FriBox/Air-Sensor/HardWare/ESP32-D0WDQ6-1.png

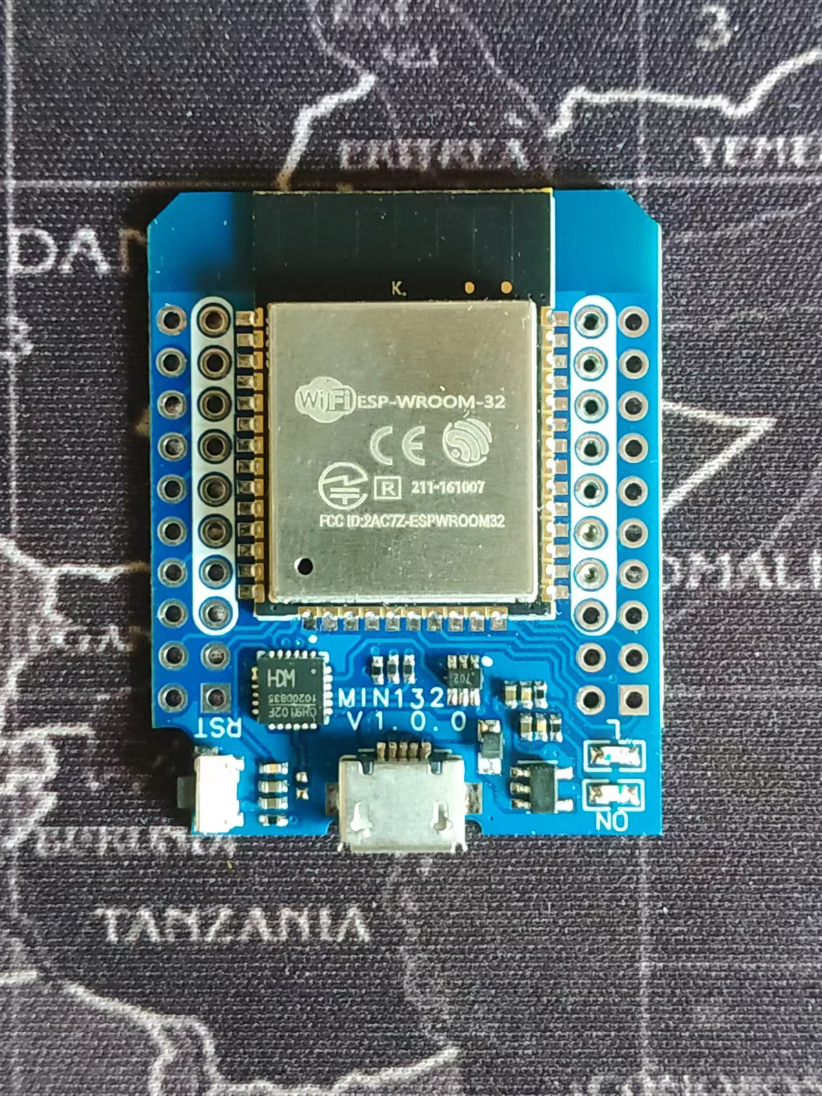
HardWare/ESP32-D0WDQ6-1.png
