FriBox/Air-Sensor/HardWare/ESP32-D0WDQ6-2.png

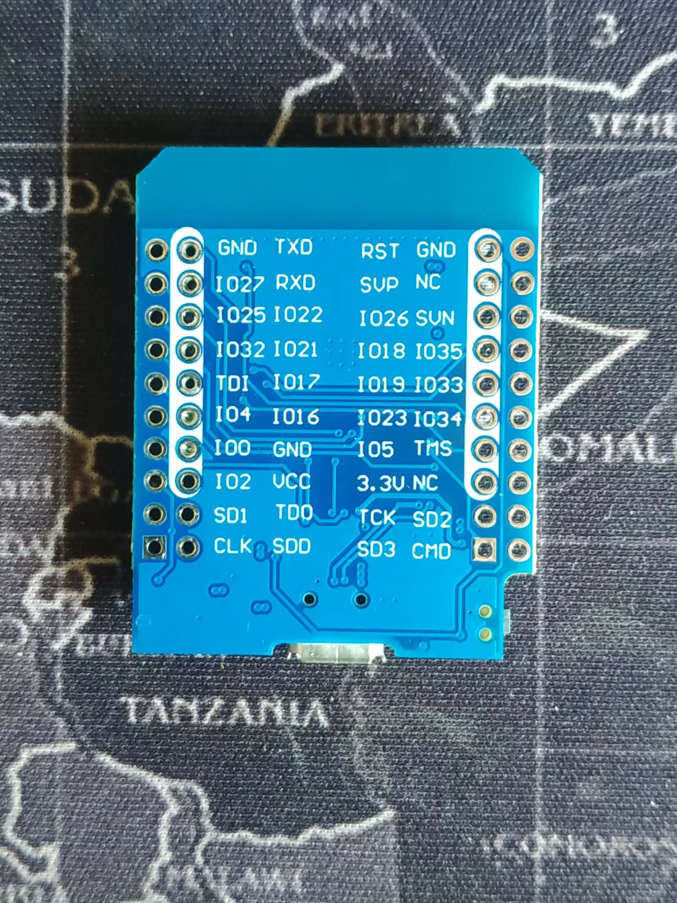
HardWare/ESP32-D0WDQ6-2.png
