FriBox/Air-Sensor/HardWare/PMS5003ST-2.png

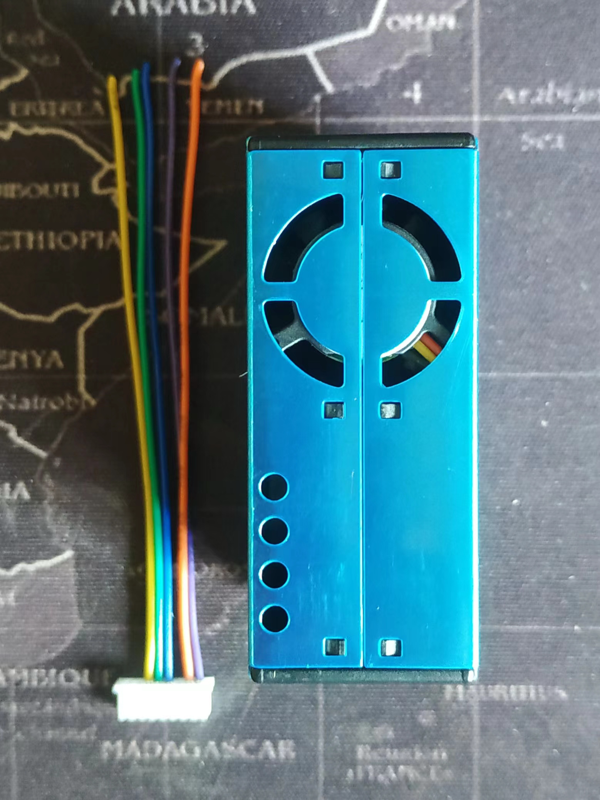
HardWare/PMS5003ST-2.png
