FriBox/Air-Sensor/HardWare/TJC4832T035_011-1.png

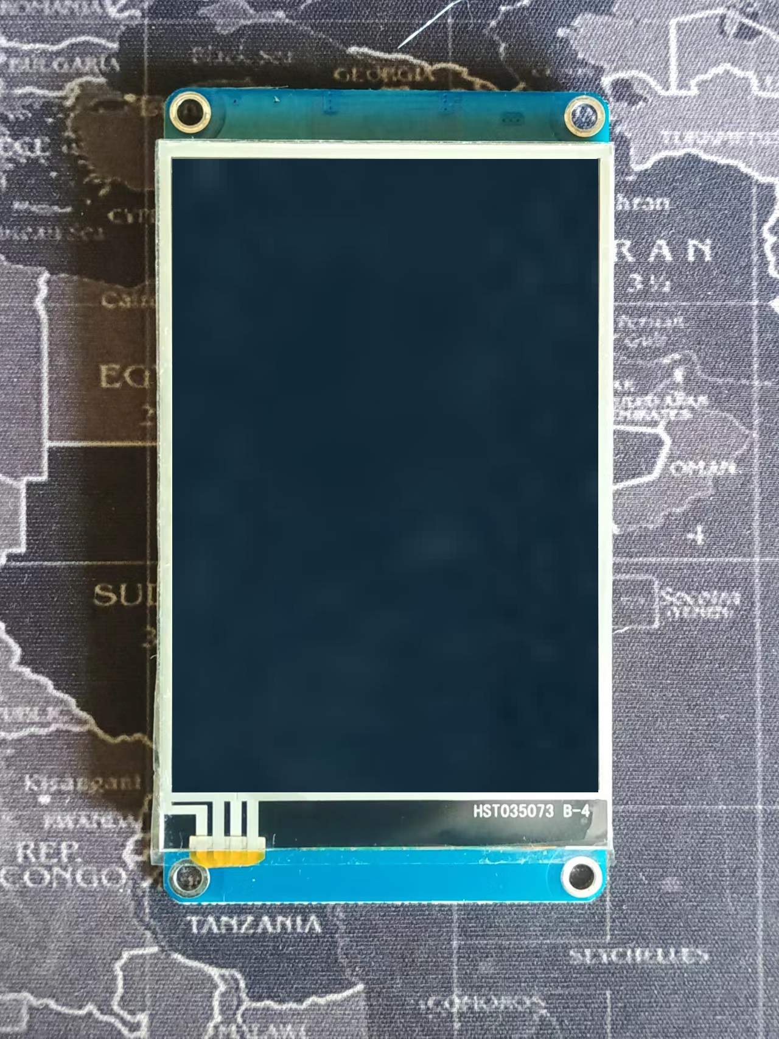
HardWare/TJC4832T035_011-1.png
